tvelliott/dsp_ice/firmware/bh_fft_win.c

//MIT License
//
//Copyright (c) 2017 tvelliott
//
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
//octave> win=blackmanharris(512)
const float fft_win_512[] = {
6.000000000000102e-05, 6.213934408222897e-05, 6.856681787752866e-05,
7.931074596204991e-05, 9.441833571863234e-05, 0.0001139556769343061,
0.0001380077411611315, 0.000166678380766937, 0.0002000903275801384,
0.0002383851910115475, 0.000281723455517368, 0.0003302844772450492,
0.0003842664796848607, 0.0004438865481300423, 0.0005093806227297864,
0.000581003489899104, 0.0006590287718329872, 0.0007437489138522185,
0.0008354751692946742, 0.0009345375816437341, 0.001041284963575627,
0.001156084872586477, 0.001279323582849629, 0.001411406052936706,
0.001552755889024511, 0.001703815303196113, 0.001865045066434716,
0.002036924455895553, 0.002219951196033854, 0.002414641393155894,
0.002621529462953552, 0.002841168050574135, 0.003074127942772893,
0.003320997971688778, 0.003582384909780979, 0.003858913355460197,
0.004151225608946042, 0.004459981537882324, 0.004785858432239458,
0.005129550848037455, 0.005491770439421704, 0.005873245778630113,
0.006274722163391908, 0.006696961411304985, 0.007140741640745144,
0.007606857037867643, 0.008096117609270552, 0.008609348919898117,
0.0091473918157748, 0.009711102131170206, 0.01030135037981053,
0.01091902142976361, 0.01156501416164109, 0.01224024110977683,
0.01294562808605773, 0.01368211378610016, 0.01445064937748513,
0.01525219806978507, 0.01608773466613484, 0.01695824509612209,
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
0.002029914683912826, 0.002074429819856317, 0.002119646196333833,
0.002165571795090397, 0.002212214669133876, 0.002259582942663726,
0.002307684810998831, 0.002356528540503072, 0.002406122468509024,
0.002456475003240146, 0.002507594623730806, 0.002559489879744331,
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
};
