tvelliott/dsp_ice/firmware/fpga_image.h

//filename: fpga/src/fpga_top.bin
//input file length: 135100
//compressed len: 57311
const uint8_t rle_compressed_fpga_image[] = {
0xff,0x00,0x00,0x00,0xff,0x7e,0xaa,0x99,0x7e,0x51,0x00,0x01,0x05,0x92,0x00,0x20,0x62,0x03,0x67,0x72,0x01,0x10,0x82,0x00,0x00,0x00,0x11,0x00,0x01,0x01,0x00,0x00,0x00,
0x1b,0x02,0x00,0x00,0x04,0x08,0x00,0x00,0x17,0x80,0x00,0x00,0x0a,0x08,0x00,0x00,0x04,0x20,0x00,0x00,0x8e,0x04,0x00,0x00,0x04,0x10,0x00,0x00,0x04,0x40,0x00,0x00,
0x03,0x01,0x00,0x00,0x04,0x04,0x00,0x00,0x17,0x40,0x00,0x00,0x0a,0x04,0x00,0x00,0x04,0x10,0x00,0x00,0x11,0x04,0x00,0x00,0x8e,0x02,0x00,0x00,0x04,0x08,0x00,0x00,
0x01,0x20,0x00,0x00,0x13,0x80,0x08,0x00,0x02,0x00,0x00,0x07,0x08,0x00,0x00,0x04,0x20,0x00,0x00,0x39,0x0c,0x00,0x00,0x02,0x30,0x00,0x30,0x00,0x00,0x14,0x09,0x00,
0x03,0x00,0x00,0x0b,0x10,0x00,0x00,0x04,0xc0,0x00,0x00,0x7a,0x04,0x00,0x00,0x0d,0x08,0x00,0x00,0x6d,0x10,0x00,0x00,0x4c,0x02,0x00,0x00,0x0b,0x10,0x00,0x00,0xca,
0x01,0x00,0x00,0x67,0x80,0x00,0x00,0x0e,0x04,0x00,0x00,0x1f,0x0e,0x00,0x00,0x31,0x01,0xc0,0x00,0x00,0x35,0x02,0x00,0x00,0x32,0x20,0x00,0x00,0x02,0x40,0x00,0x00,
0x1d,0x10,0x00,0x00,0x04,0x40,0x00,0x00,0x03,0x01,0x00,0x00,0x04,0x04,0x00,0x00,0x04,0x10,0x00,0x00,0x16,0x01,0x00,0x00,0x0a,0x08,0x10,0x00,0x00,0x04,0x40,0x00,
0x00,0x02,0x0f,0x00,0x00,0x0c,0x10,0x00,0x00,0x4e,0x78,0x00,0x00,0x09,0x80,0x08,0x00,0x00,0x0b,0x38,0x00,0x00,0x36,0x72,0x00,0x00,0x01,0x10,0x00,0x00,0x05,0x04,
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
0x00,0x24,0x04,0x00,0x00,0x2a,0x15,0x00,0x02,0x00,0x00,0x0d,0x10,0x1e,0x68,0x00,0x00,0x01,0x40,0x00,0x00,0x17,0x20,0x00,0x00,0x19,0x02,0x00,0x00,0x15,0x2c,0x00,
0x00,0x04,0xa0,0x80,0x00,0x08,0x00,0x00,0x06,0x01,0x00,0x00,0x03,0x10,0x03,0x41,0x40,0x00,0x01,0x29,0x00,0x00,0x41,0x01,0x80,0x01,0x98,0x00,0x00,0x01,0x06,0x00,
0x21,0x69,0x61,0x01,0x00,0x00,0x03,0x04,0x02,0x00,0x00,0x0c,0x06,0x10,0x1c,0x70,0x00,0x00,0x14,0x04,0x00,0x00,0x04,0x08,0x00,0x00,0x0a,0x04,0x00,0x00,0x1d,0x89,
0x00,0x00,0x03,0x04,0x03,0x6a,0x00,0x01,0x00,0x00,0x02,0x28,0x00,0x00,0x0e,0x10,0x1e,0x43,0x40,0x00,0x00,0x13,0x0e,0x00,0x00,0x2e,0x03,0x00,0x03,0x99,0x18,0x40,
0x40,0x00,0x04,0x00,0x1e,0x05,0xca,0xa0,0x41,0x00,0x00,0x02,0x20,0xcc,0x00,0x00,0x06,0x41,0x00,0x00,0x03,0x04,0x00,0x84,0x30,0x00,0x00,0x45,0x01,0x00,0x00,0x00,
0x08,0x52,0x40,0x08,0x04,0x00,0x36,0x2a,0xea,0x90,0x01,0x00,0x00,0x01,0xc0,0x27,0x30,0x00,0x00,0x06,0x20,0x01,0x00,0x00,0x02,0x0c,0x01,0x40,0x38,0xc0,0x00,0x00,
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
