tvelliott/dsp_ice/firmware/uart3.c

//MIT License
//
//Copyright (c) 2017 tvelliott
//
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
#include <stdint.h>
#include <string.h>
#include <stdio.h>

#include "stm32f4xx_gpio.h"
#include "stm32f4xx_usart.h"
#include "stm32f4xx_rcc.h"
#include "stm32f4xx_exti.h"
#include "misc.h"
#include "std_io.h"
#include "uart3.h"

#define MAX_STRLEN 256
static volatile int cmd_out_index;
static volatile uint8_t cmd_buffer[256];
static int8_t did_init;

/////////////////////////////////////////////////////////////////////////////////
/////////////////////////////////////////////////////////////////////////////////
void uart3_init(int32_t br)
{
  USART_InitTypeDef USART_InitStructure;
  GPIO_InitTypeDef GPIO_InitStructure;
  NVIC_InitTypeDef   NVIC_InitStructure;

  RCC_APB1PeriphClockCmd(RCC_APB1Periph_USART3, ENABLE);

  GPIO_InitStructure.GPIO_Speed = GPIO_Speed_50MHz;
  GPIO_InitStructure.GPIO_OType = GPIO_OType_PP;  
  GPIO_InitStructure.GPIO_PuPd = GPIO_PuPd_UP;  

  GPIO_InitStructure.GPIO_Mode = GPIO_Mode_AF; 
  GPIO_InitStructure.GPIO_Pin = GPIO_Pin_10;
  GPIO_Init(GPIOB, &GPIO_InitStructure);

  GPIO_InitStructure.GPIO_Mode = GPIO_Mode_AF; 
  GPIO_InitStructure.GPIO_Pin = GPIO_Pin_11;
  GPIO_Init(GPIOB, &GPIO_InitStructure);

  GPIO_PinAFConfig( GPIOB, GPIO_PinSource10, GPIO_AF_USART3);
  GPIO_PinAFConfig( GPIOB, GPIO_PinSource11, GPIO_AF_USART3);

  USART_DeInit(USART3);

  USART_InitStructure.USART_BaudRate = br;

  USART_InitStructure.USART_StopBits = USART_StopBits_1;

  USART_InitStructure.USART_Parity = USART_Parity_No;

  USART_InitStructure.USART_WordLength = USART_WordLength_8b;

  USART_InitStructure.USART_HardwareFlowControl = USART_HardwareFlowControl_None;
  USART_InitStructure.USART_Mode = USART_Mode_Tx | USART_Mode_Rx;
  USART_Init(USART3, &USART_InitStructure);

  USART_ITConfig(USART3, USART_IT_RXNE, ENABLE); // enable the USART3 receive interrupt
  USART_ITConfig(USART3, USART_IT_TC, ENABLE); // enable the USART6 transmit empty interrupt

  NVIC_InitStructure.NVIC_IRQChannel = USART3_IRQn;    // we want to configure the USART3 interrupts
  NVIC_InitStructure.NVIC_IRQChannelPreemptionPriority = 0;// this sets the priority group of the USART3 interrupts
  NVIC_InitStructure.NVIC_IRQChannelSubPriority = 0;     // this sets the subpriority inside the group
  NVIC_InitStructure.NVIC_IRQChannelCmd = ENABLE;      // the USART3 interrupts are globally enabled
  NVIC_Init(&NVIC_InitStructure);

  /* Enable USART3 */
  USART_Cmd(USART3, ENABLE);

  did_init=1;

}

///////////////////////////////////////////////////////////////////////////////////////
///////////////////////////////////////////////////////////////////////////////////////
void uart3_putc(uint16_t c)
{

  if(!did_init) return;

  /* Send some test data */
  while( !USART_GetFlagStatus(USART3, USART_FLAG_TXE) );
  USART_SendData(USART3, c);
}
//////////////////////////////////////////////////////////////////
//////////////////////////////////////////////////////////////////
void USART3_IRQHandler()
{
uint8_t buff[2];
  buff[1] = 0;

  //rx
  while( USART_GetITStatus(USART3, USART_IT_RXNE) ) {
    buff[0] = USART3->DR; 
    printf("%s",buff); //send from serial console to telnet console
  }

  //tx
  if( USART_GetITStatus(USART3, USART_IT_TC) ) {
    USART_ClearFlag(USART3, USART_FLAG_TC);

      if(cmd_buffer[cmd_out_index]!=0) {
        uart3_putc(cmd_buffer[cmd_out_index++]);
      } else {
        cmd_out_index=0;
      }
  }
}
////////////////////////////////////////////////////////////////
////////////////////////////////////////////////////////////////
void puts_u3(uint8_t *buffer, int len)
{
  memcpy(cmd_buffer,buffer,len);
  cmd_buffer[len]=0; //terminate
  uart3_putc(cmd_buffer[cmd_out_index++]);
}
